zomerfeld/ClockOclock/Process_Pics_and_Docs/IMG_1471.JPG

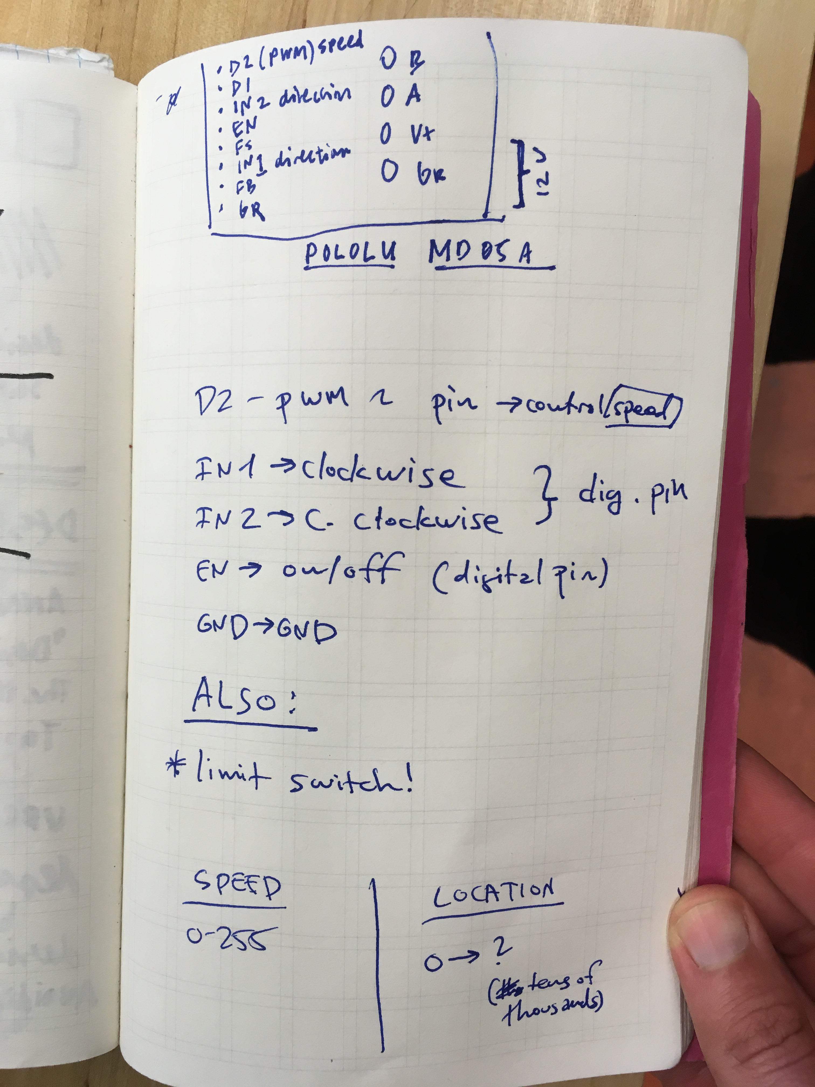
Process_Pics_and_Docs/IMG_1471.JPG
