zomerfeld/ClockOclock/Process_Pics_and_Docs/IMG_1473.JPG

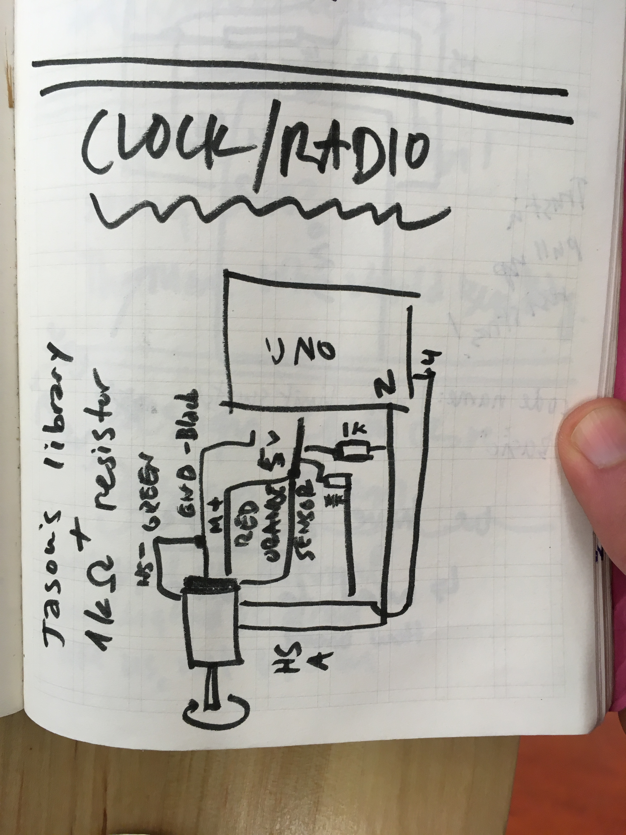
Process_Pics_and_Docs/IMG_1473.JPG
