zomerfeld/ClockOclock/Process_Pics_and_Docs/IMG_1474.JPG

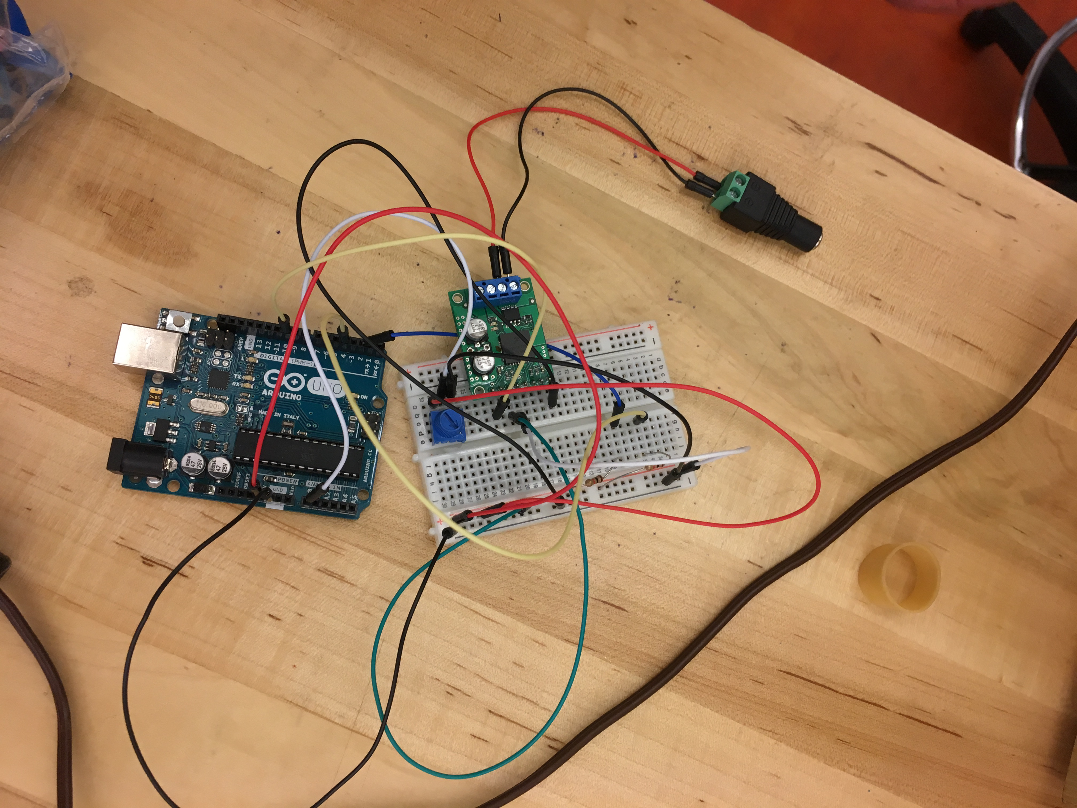
Process_Pics_and_Docs/IMG_1474.JPG
