zomerfeld/ClockOclock/Process_Pics_and_Docs/IMG_4266.JPG

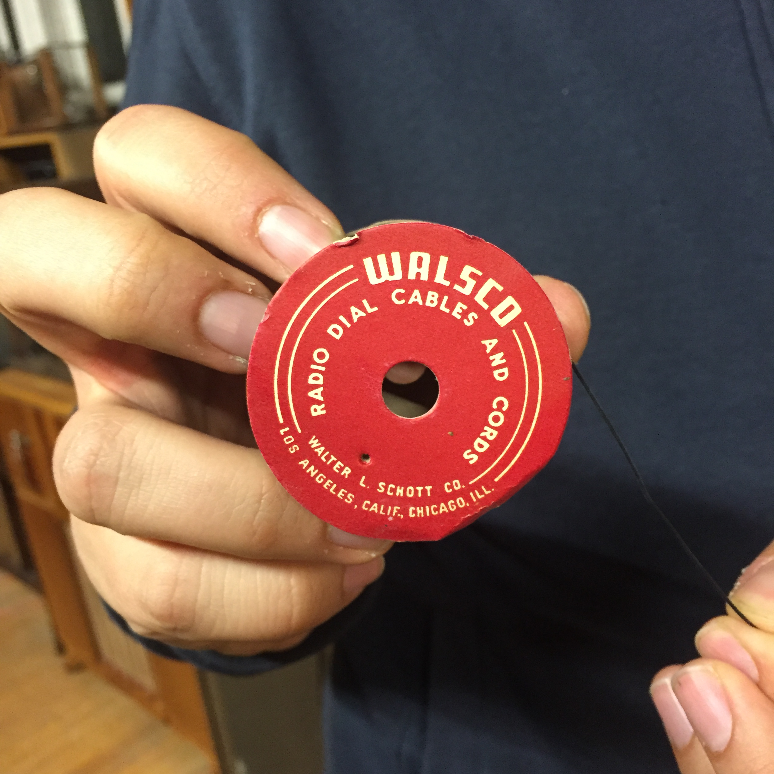
Process_Pics_and_Docs/IMG_4266.JPG
