zomerfeld/ClockOclock/Process_Pics_and_Docs/IMG_5357.JPG

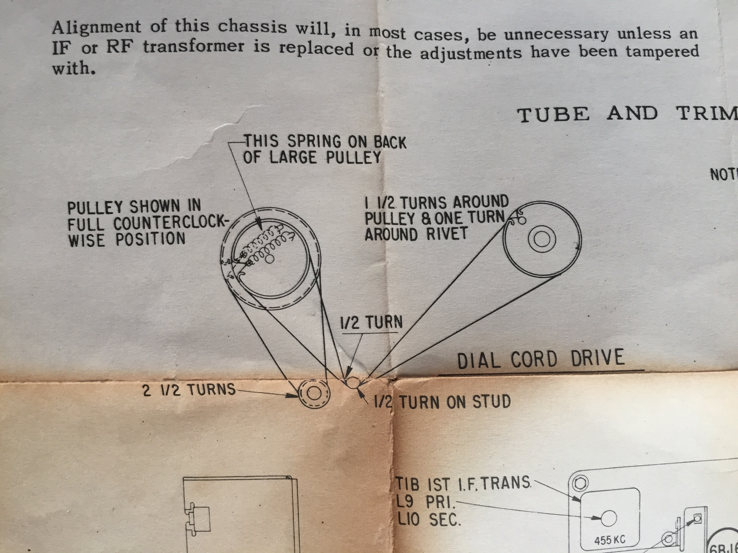
Process_Pics_and_Docs/IMG_5357.JPG
