zomerfeld/ClockOclock/Process_Pics_and_Docs/IMG_5429.JPG

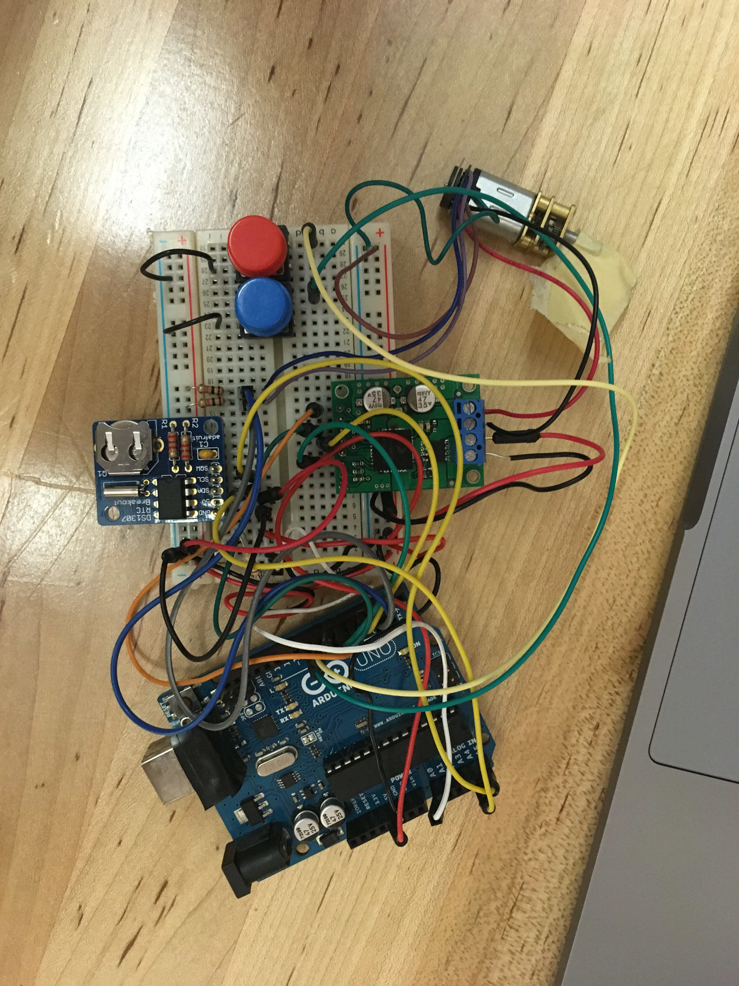
Process_Pics_and_Docs/IMG_5429.JPG
